walclu/smartReflow/Pictures/PCB/PCB1.png

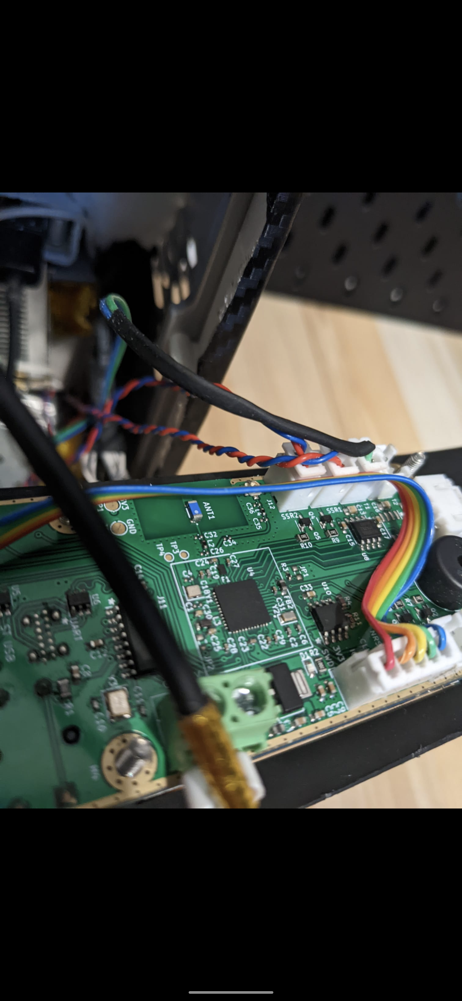
Pictures/PCB/PCB1.png
