walclu/smartReflow/Pictures/PCB/PCB2.png

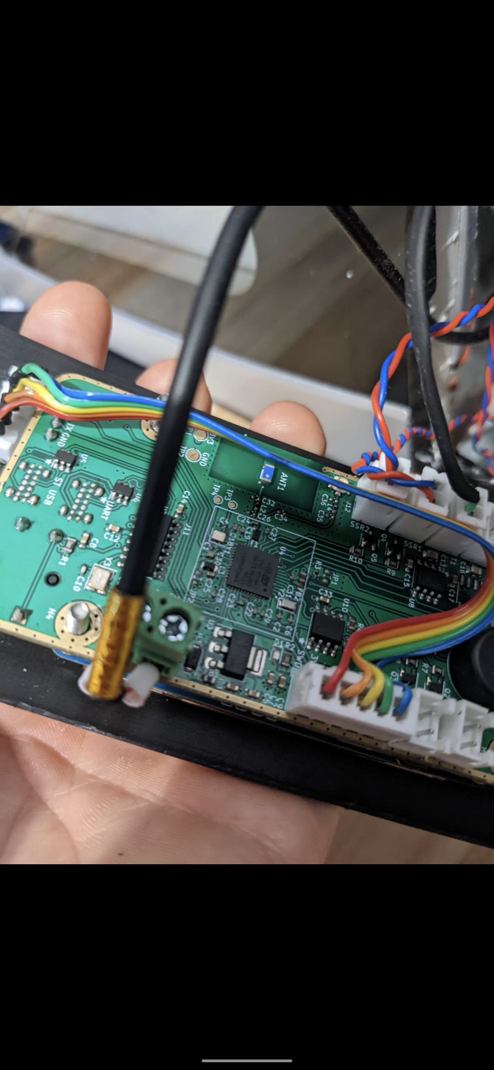
Pictures/PCB/PCB2.png
