walclu/smartReflow/Pictures/Results/Soldering2.png

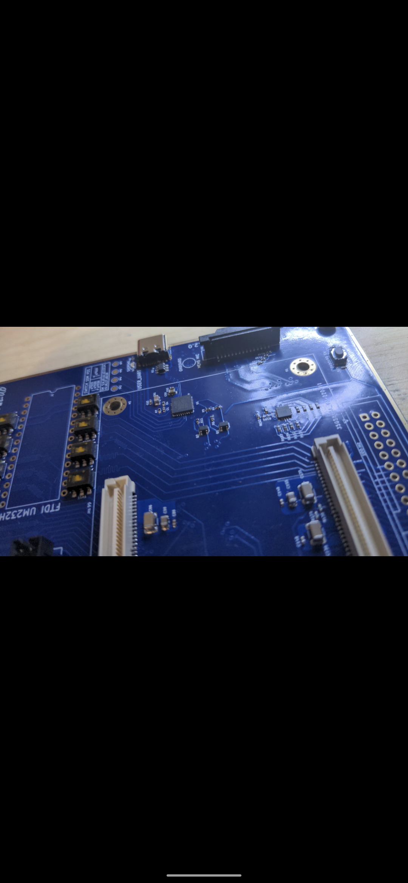
Pictures/Results/Soldering2.png
